zenitheesc/garatea2/Software/BUZZ/BUZZ.h

//
//  BUZZ.hpp
//  testec ARDUINO
//
//  Created by Danilo Oliveira on 11/10/16.
//  Copyright © 2016 Danilo Oliveira. All rights reserved.
//

#ifndef BUZZ_h
#define BUZZ_h

#include <stdio.h>
#include <Arduino.h>

class BUZZ
{
public:
    BUZZ(int buzzPin);
    ~BUZZ();
    
    enum{
        ON,
        OFF
    };
    
    void beep(void); // Toque intermitente a cada segundo
    void beeper(int n); //
    int getBuzzPin();
private:
    int buzzPin = 4; // Information for some function who needs this
};


#endif /* BUZZ_hpp */
